MickTheMechanic/Tire_Tool/Code/RES/backgroundV2.bmp

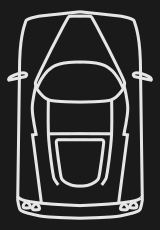
Code/RES/backgroundV2.bmp
