MickTheMechanic/Tire_Tool/Code/RES/GaugeV3_220x220.bmp

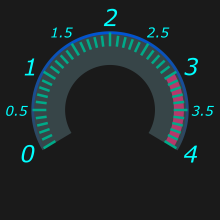
Code/RES/GaugeV3_220x220.bmp
